vapoduino/vapoduino_fatty/images/button.jpg

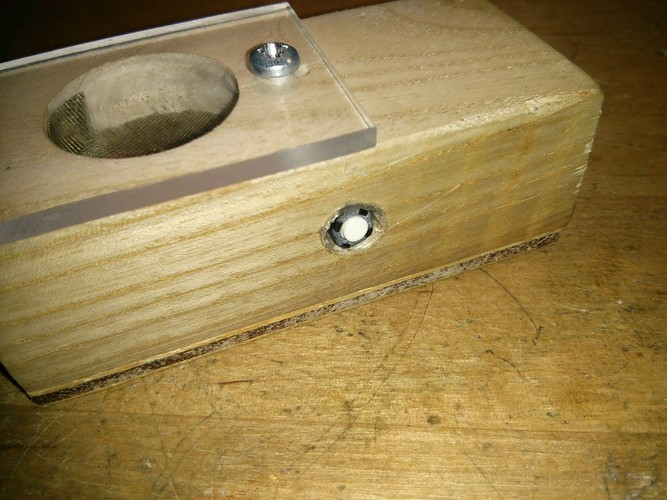
images/button.jpg
