vapoduino/vapoduino_fatty/images/coil.jpg

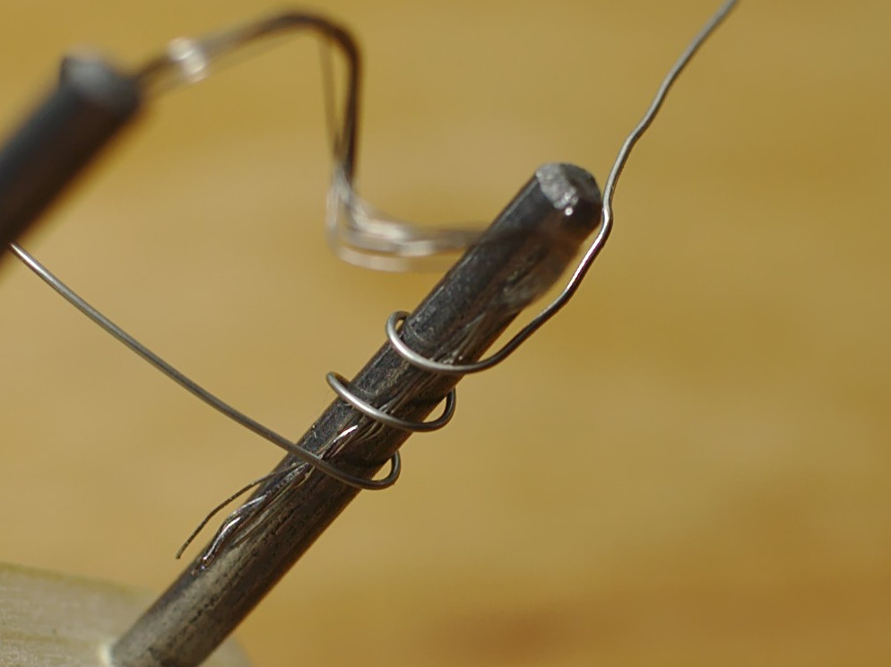
images/coil.jpg
