vapoduino/vapoduino_fatty/images/coil_connection.jpg

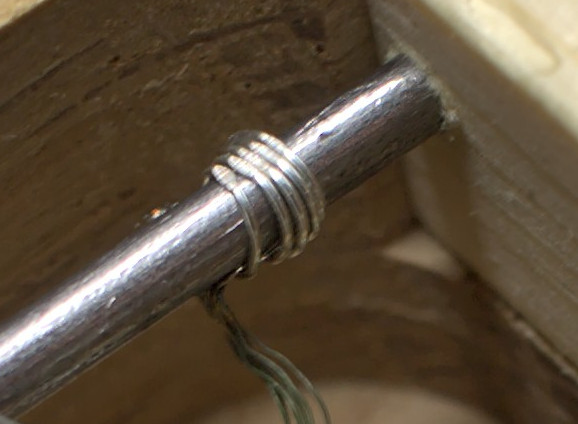
images/coil_connection.jpg
