vapoduino/vapoduino_fatty/images/mesh.jpg

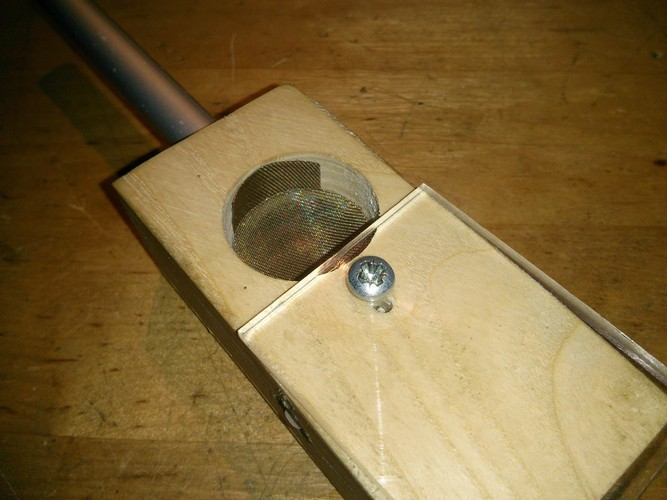
images/mesh.jpg
