vapoduino/vapoduino_fatty/images/winding.jpg

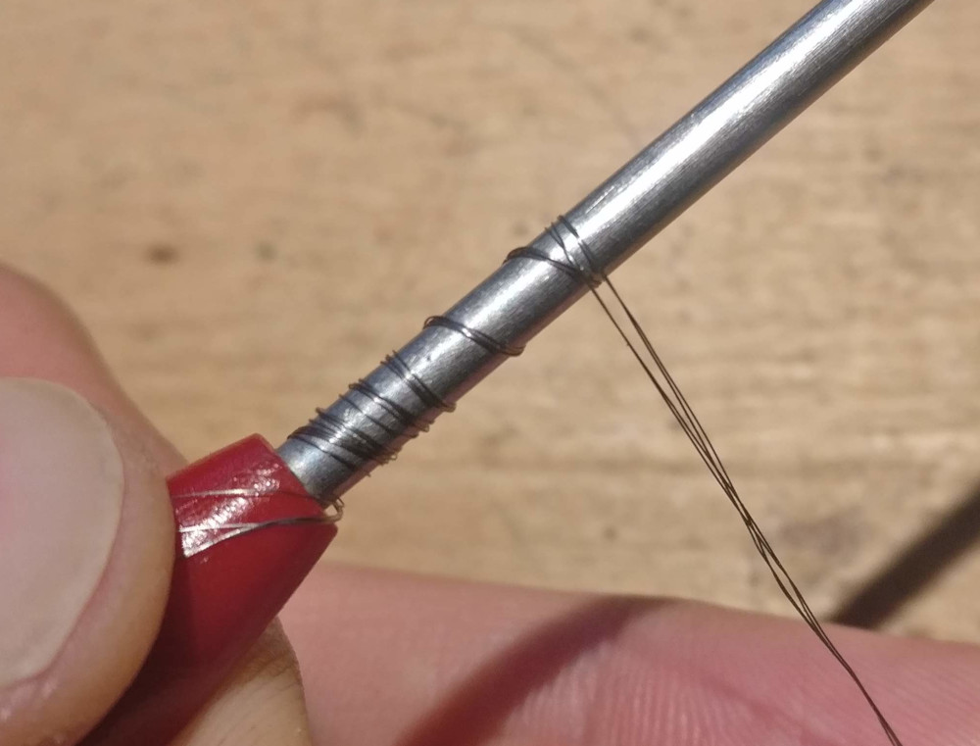
images/winding.jpg
