vapoduino/vapoduino_fatty/images/step_02.png

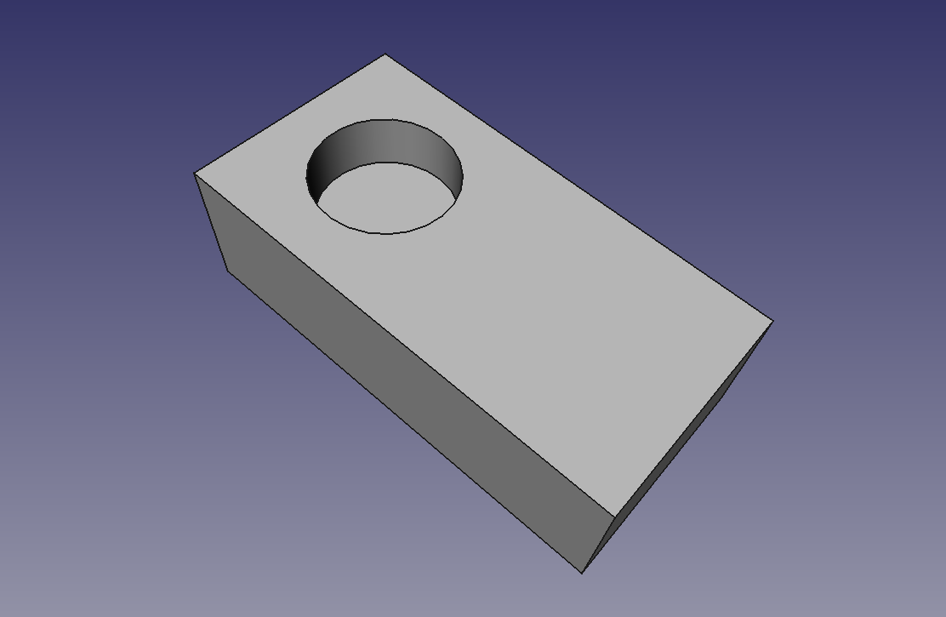
images/step_02.png
