vapoduino/vapoduino_fatty/images/step_04.png

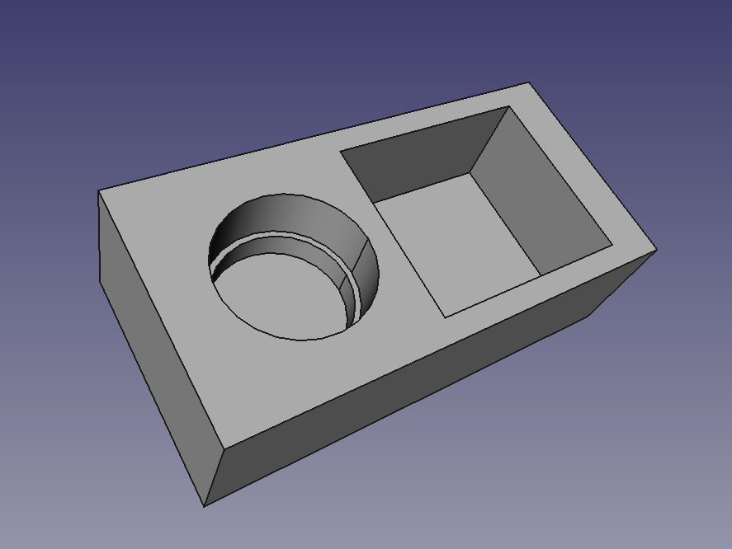
images/step_04.png
