vapoduino/vapoduino_fatty/images/step_05.png

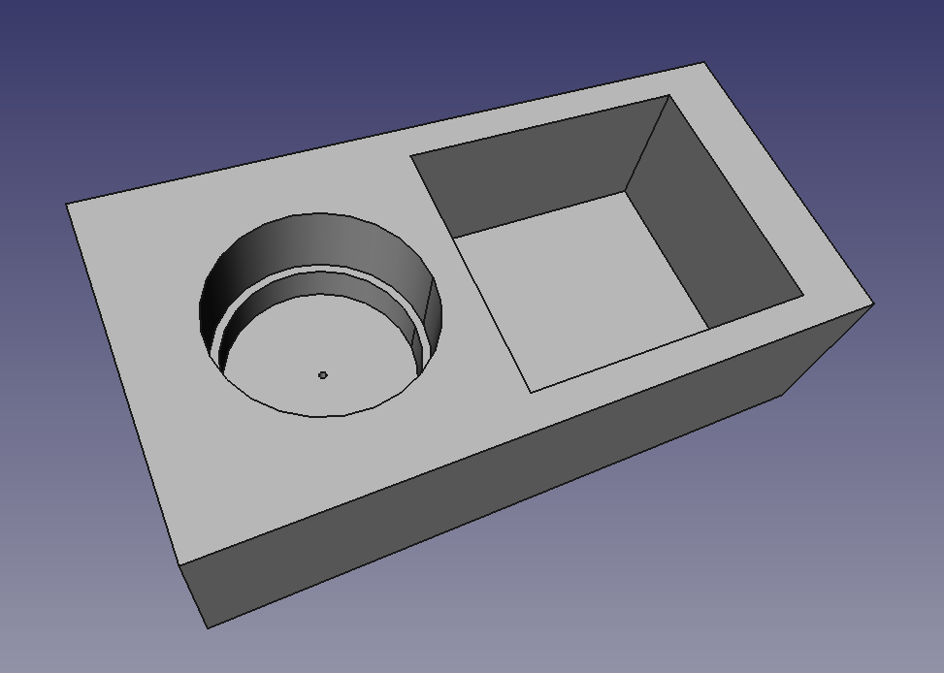
images/step_05.png
