vapoduino/vapoduino_fatty/images/step_06.gif

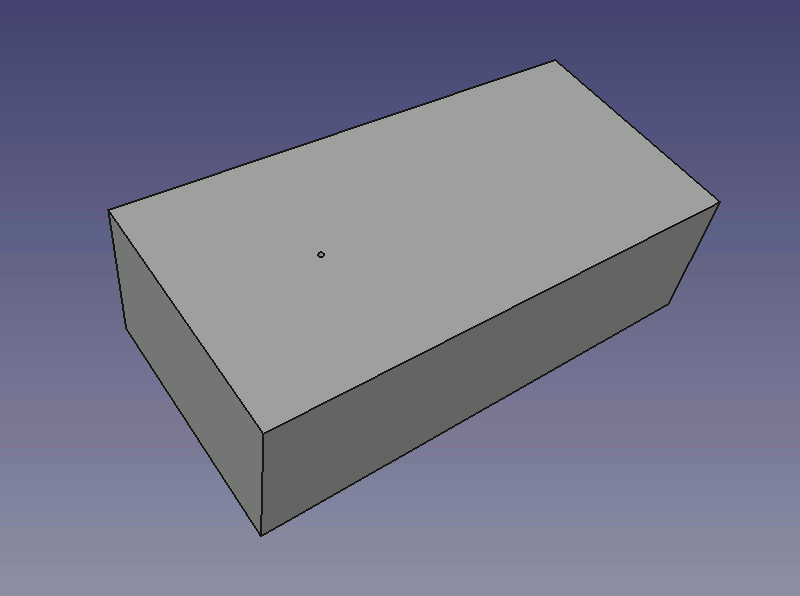
images/step_06.gif
