vapoduino/vapoduino_fatty/images/step_07.png

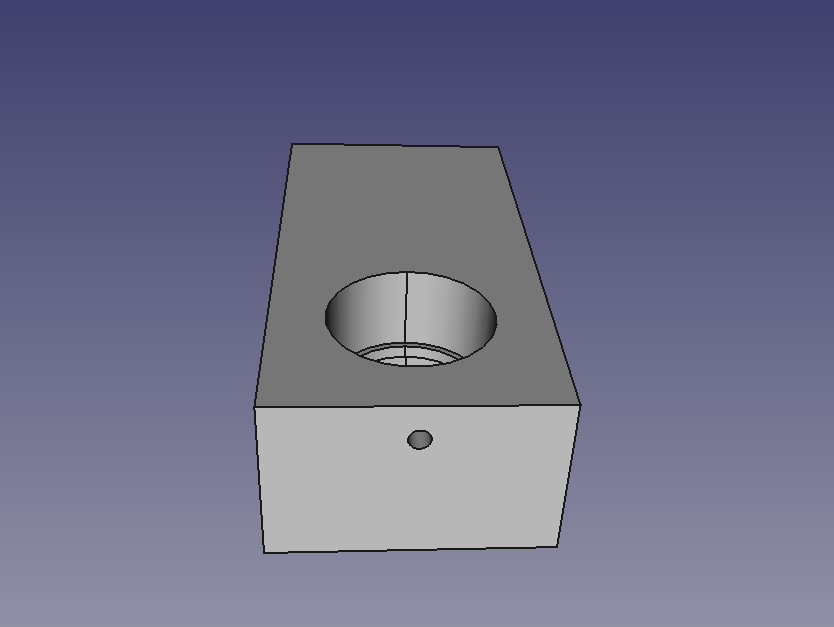
images/step_07.png
