vapoduino/vapoduino_fatty/images/step_09.png

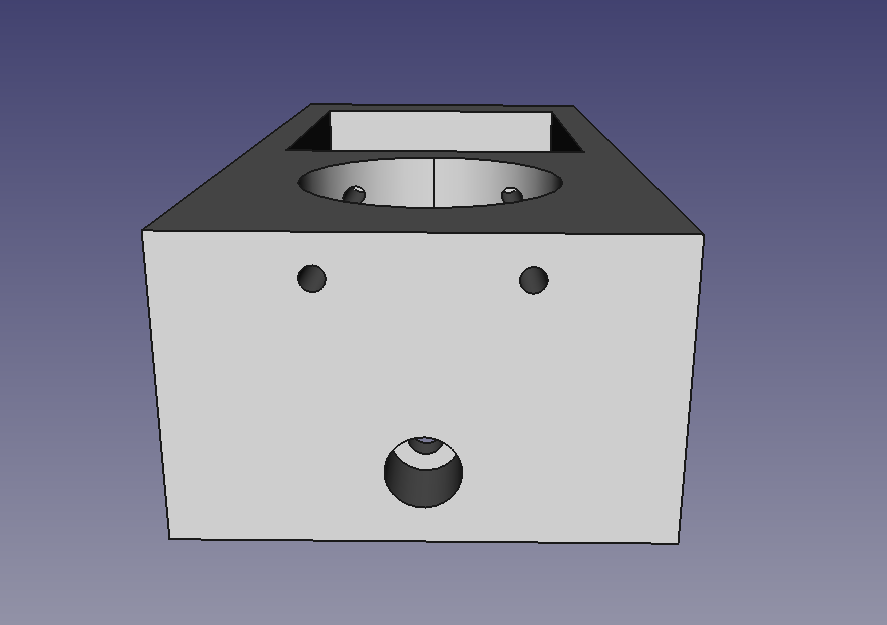
images/step_09.png
