vapoduino/vapoduino_fatty/images/step_10.png

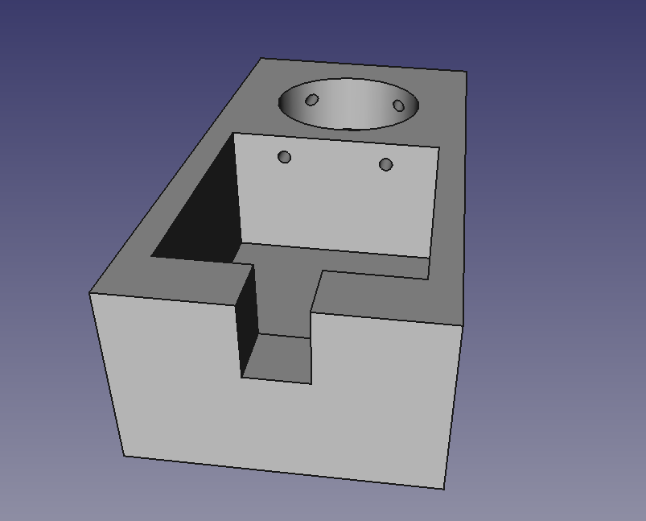
images/step_10.png
