vapoduino/vapoduino_fatty/images/step_11.png

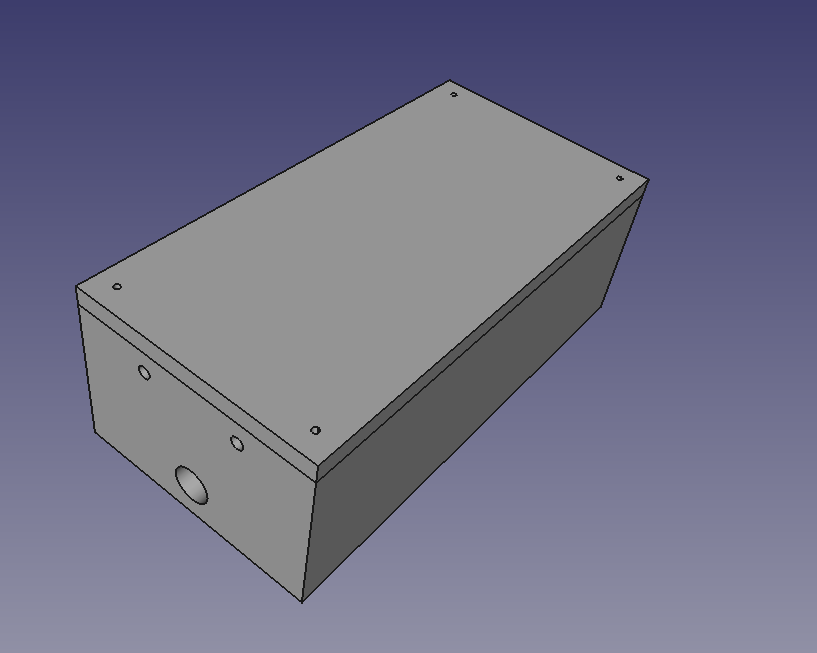
images/step_11.png
